AndresBercovich/OpenLamborghino/Tutoriales/Tutorial_1_PERIFERICOS/Control_Angular.ino

int setpoint = 0;
int last_error = 0;
int pot_limite = 250;

int PIDLambo(int pos, float Kp, float Kd) {

  int error = pos - setpoint;
  int derivative = error - last_error;
  last_error = error;
  int pot_giro = (error * Kp + derivative * Kd);



  if (pot_giro > pot_limite)
    pot_giro = pot_limite;
  else if (pot_giro < -pot_limite)
    pot_giro = -pot_limite;
  return pot_giro;


}
